abeljim/violet/software/extra/tca9555/test.py

import smbus 

bus = smbus.SMBus(1)
bus.write_byte_data(32, 3, 8)
# bus.write_byte_data(32, 7, 0)
b = bus.read_byte_data(32, 3)
print(b)
#b = bus.write_byte_data(32, 3, 0)
#b = bus.write_byte_data(32, 7, 0)
bus.close()
